wntrblm/Big_Honking_Button/user_guide/docs/images/kit/2a-jacks.jpg

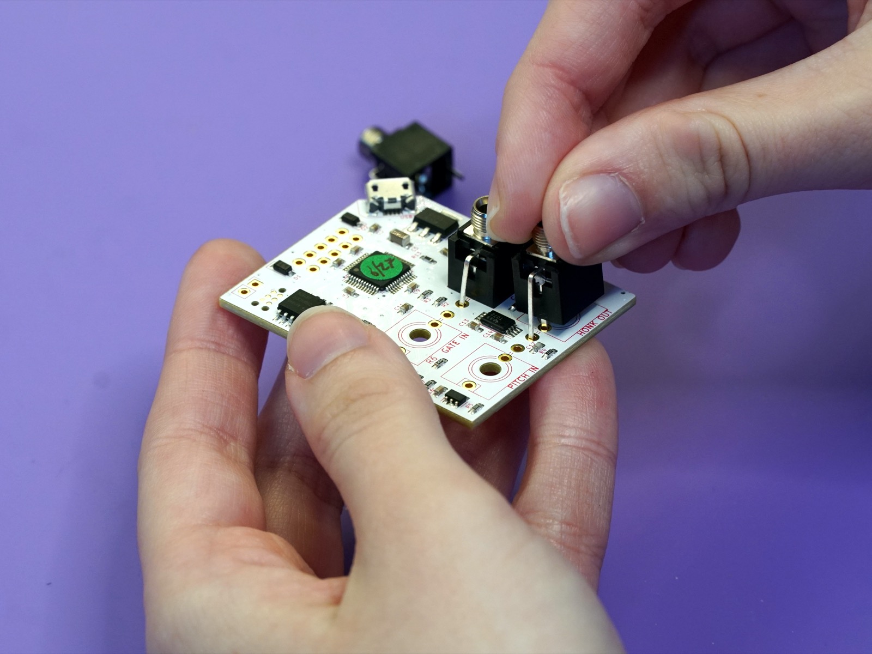
user_guide/docs/images/kit/2a-jacks.jpg
