wntrblm/Big_Honking_Button/user_guide/docs/images/kit/2c-jacks.jpg

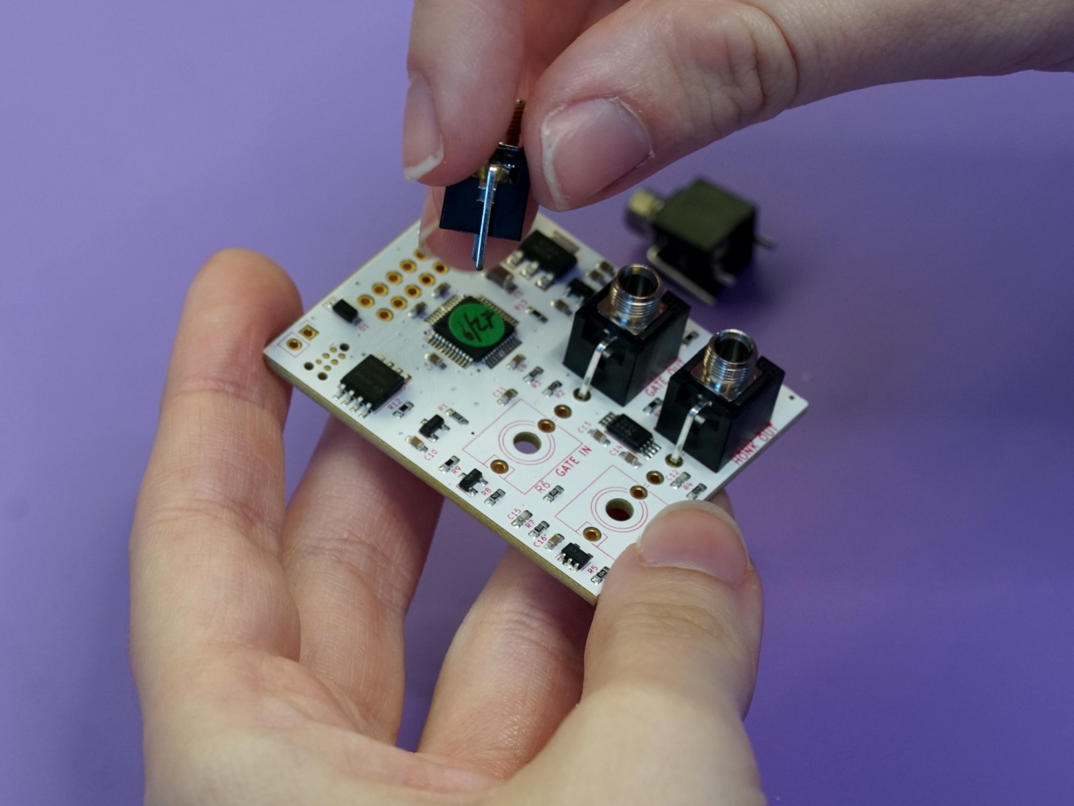
user_guide/docs/images/kit/2c-jacks.jpg
